DamCB/mu_spim/doc/images/all_unzoom.png

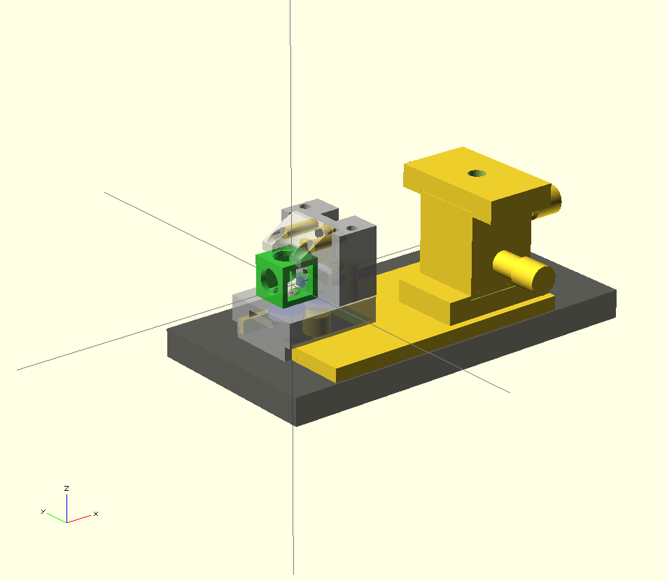
doc/images/all_unzoom.png
