DamCB/mu_spim/doc/images/all_zoom.png

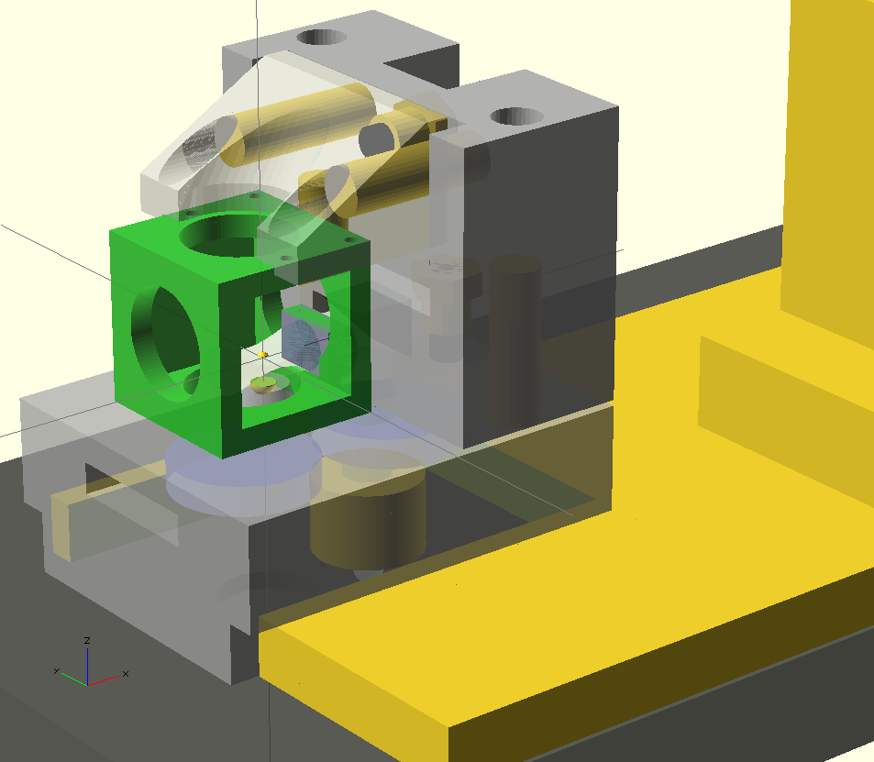
doc/images/all_zoom.png
