DamCB/mu_spim/doc/images/IMGP2774.JPG

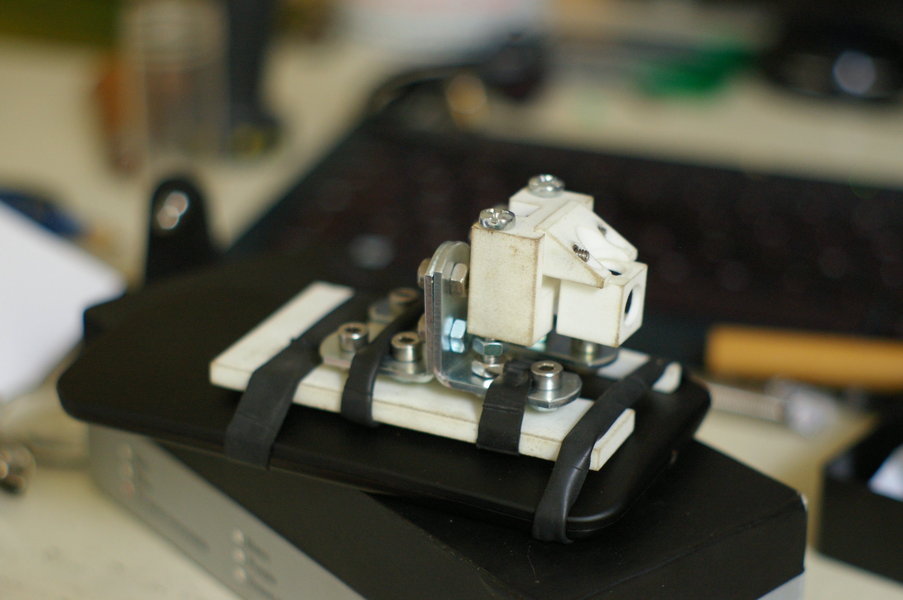
doc/images/IMGP2774.JPG
