DamCB/mu_spim/doc/images/IMGP2775.JPG

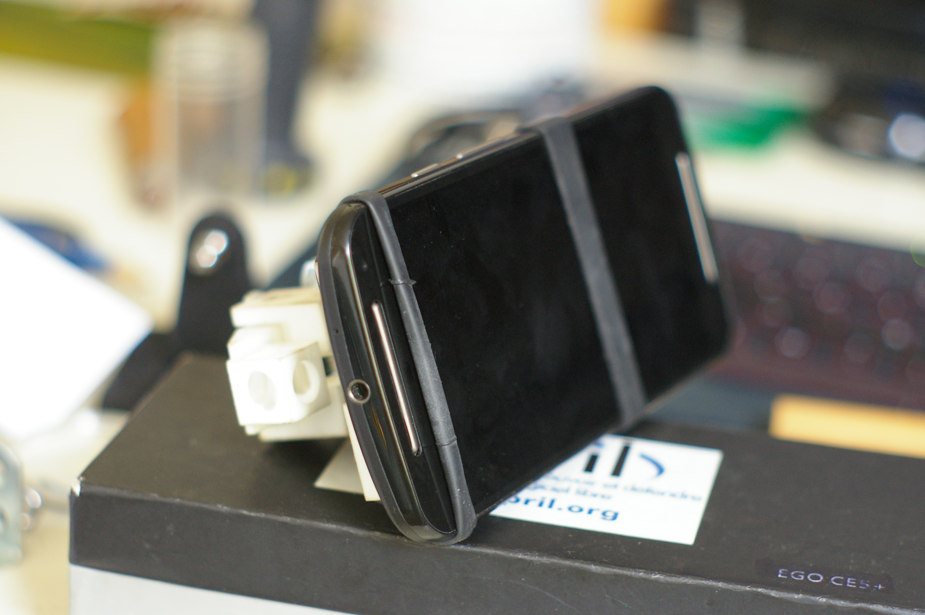
doc/images/IMGP2775.JPG
