DamCB/mu_spim/doc/images/IMGP2776.JPG

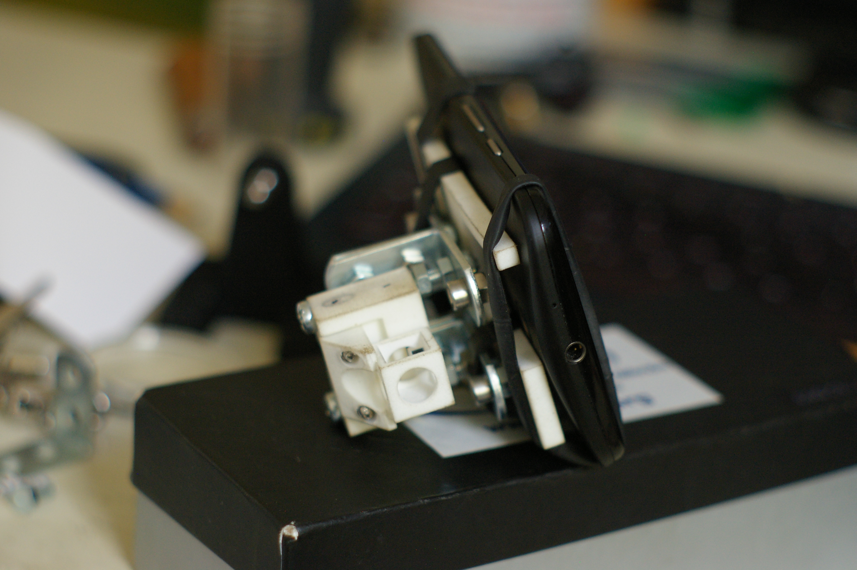
doc/images/IMGP2776.JPG
