DamCB/mu_spim/doc/images/IMGP2777.JPG

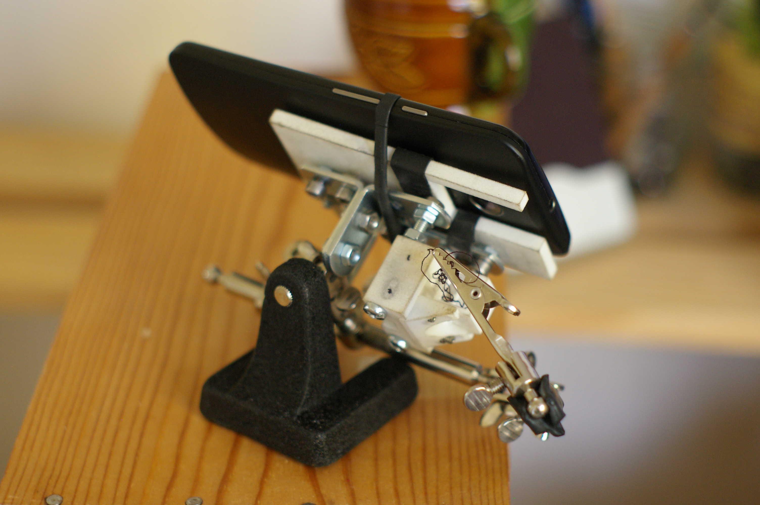
doc/images/IMGP2777.JPG
