DamCB/mu_spim/doc/images/IMGP2778.JPG

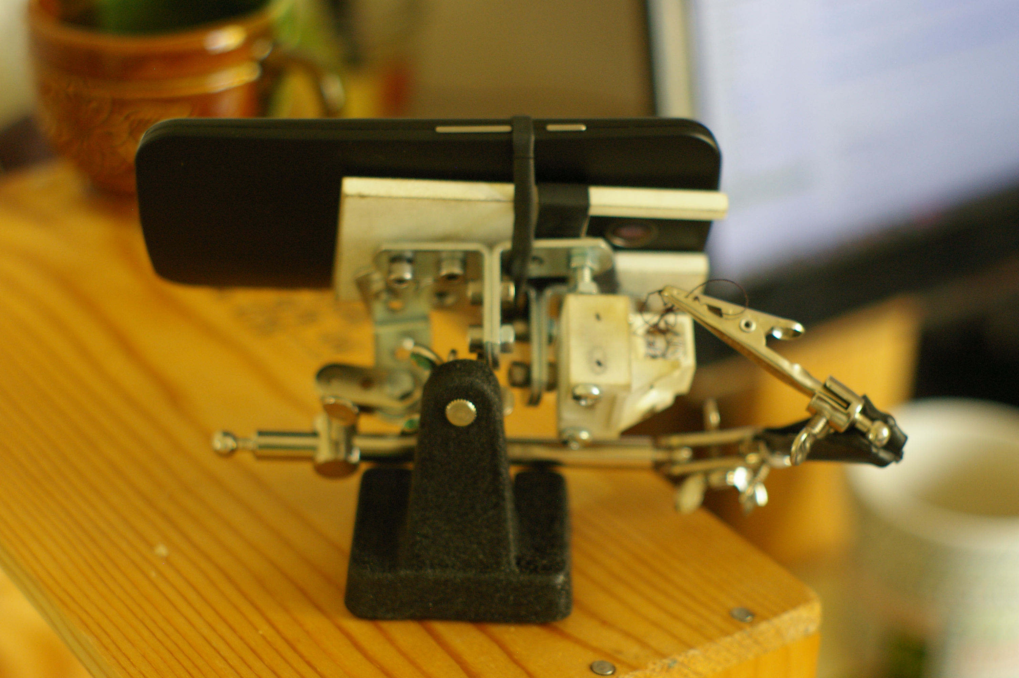
doc/images/IMGP2778.JPG
