DamCB/mu_spim/doc/images/IMGP2779.JPG

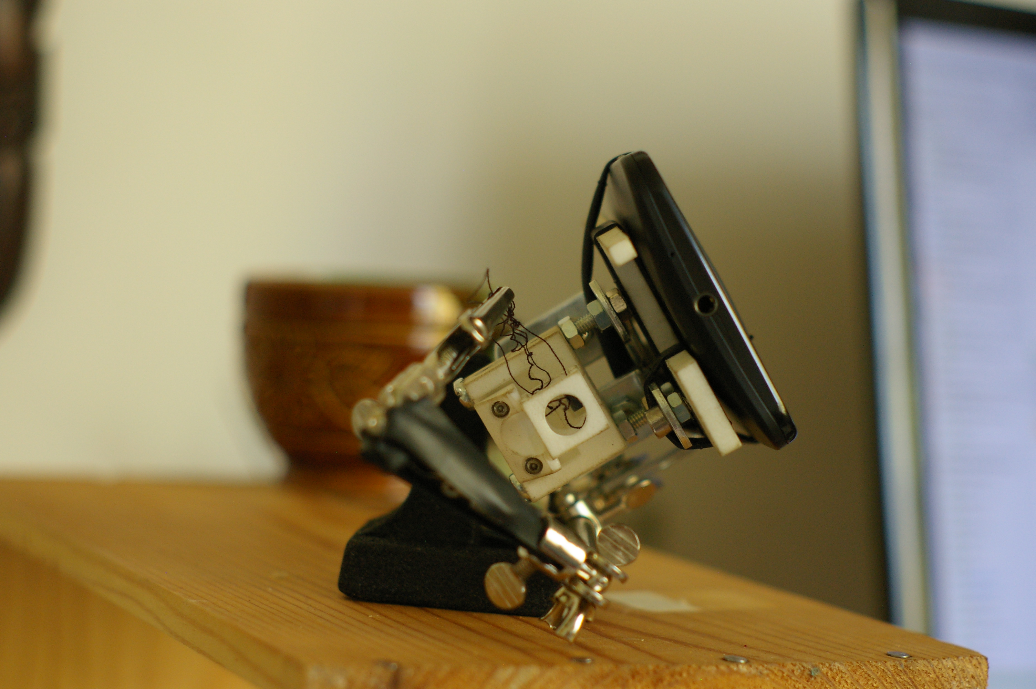
doc/images/IMGP2779.JPG
