DamCB/mu_spim/doc/images/IMGP2780.JPG

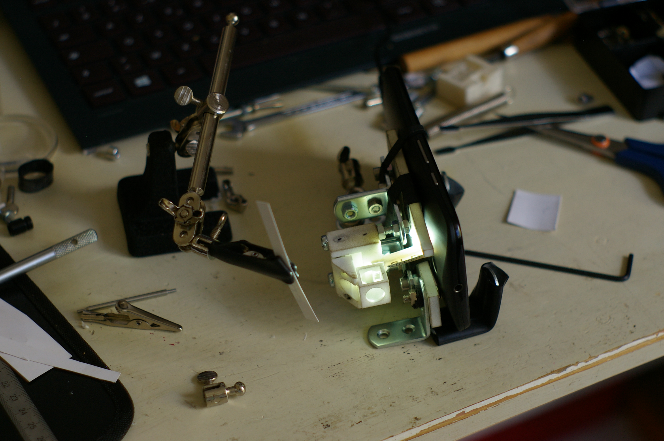
doc/images/IMGP2780.JPG
