DamCB/mu_spim/doc/images/IMGP2781.JPG

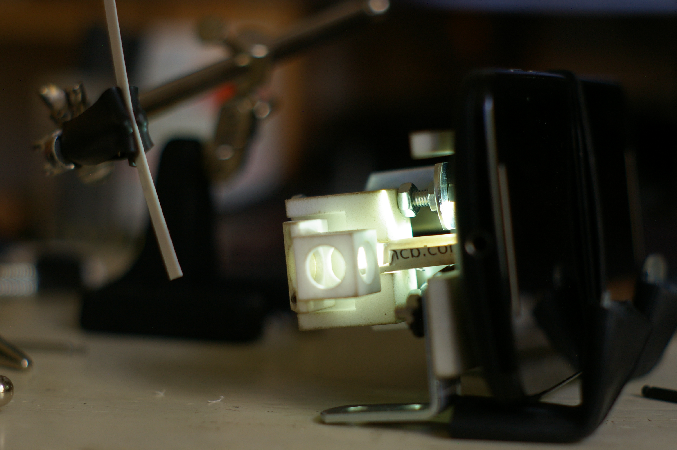
doc/images/IMGP2781.JPG
