DamCB/mu_spim/doc/images/IMGP2782.JPG

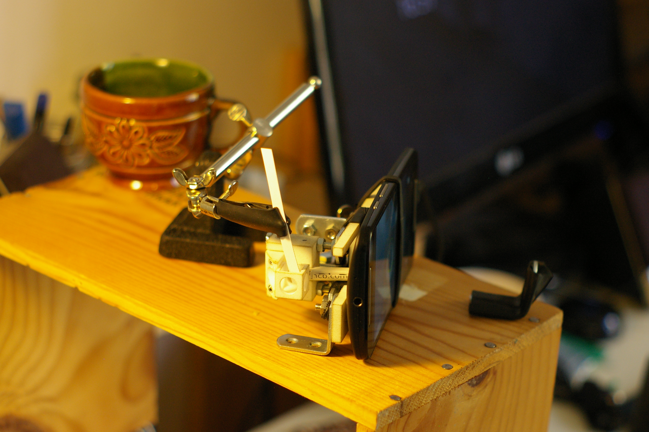
doc/images/IMGP2782.JPG
