DamCB/mu_spim/doc/images/IMGP2783.JPG

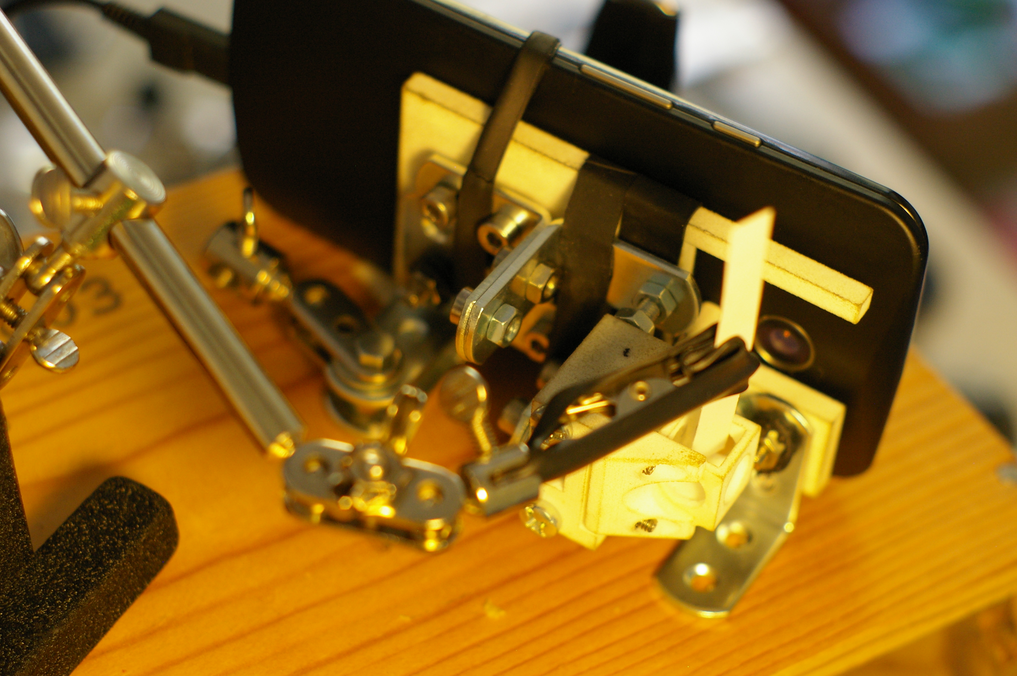
doc/images/IMGP2783.JPG
