DamCB/mu_spim/doc/images/IMGP2784.JPG

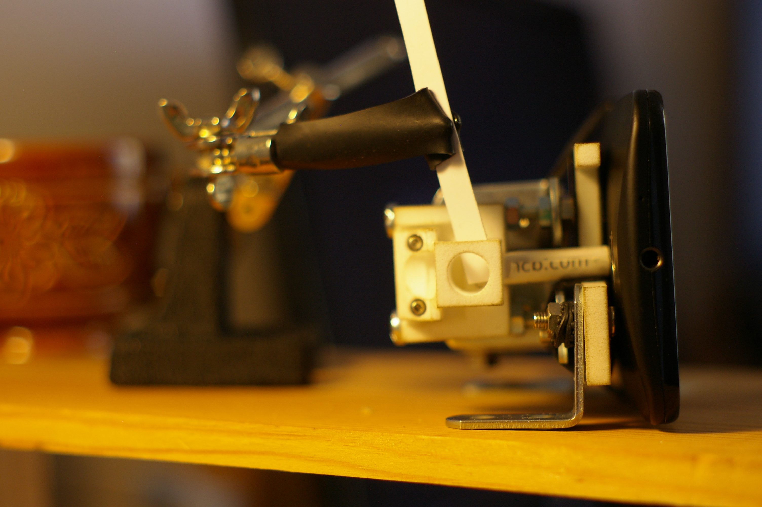
doc/images/IMGP2784.JPG
