DamCB/mu_spim/doc/images/IMGP2785.JPG

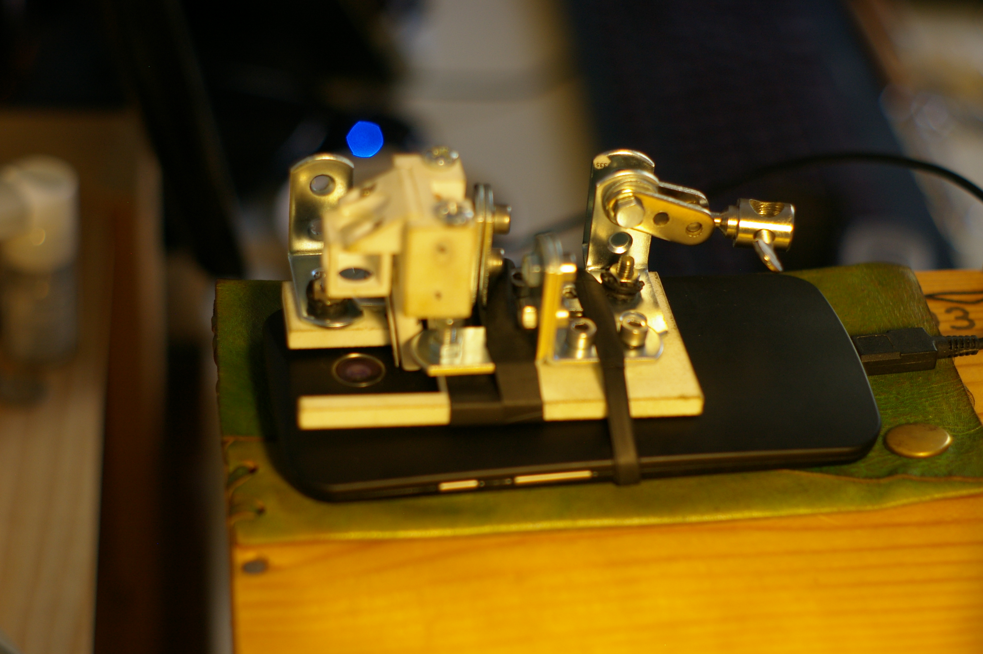
doc/images/IMGP2785.JPG
