DamCB/mu_spim/doc/images/IMGP2786.JPG

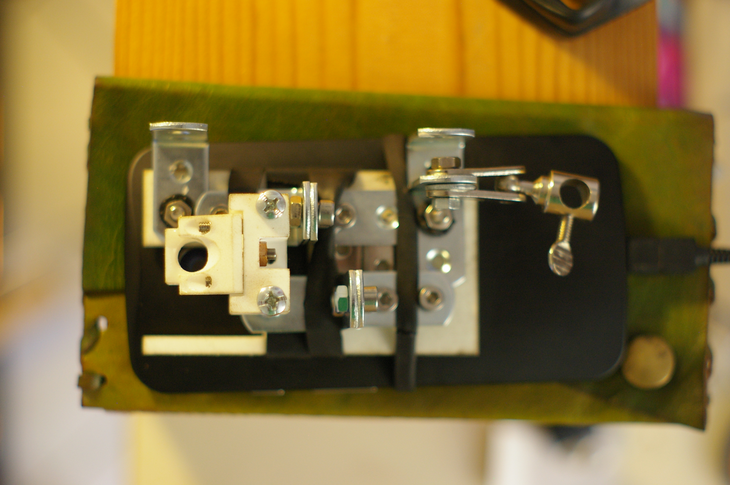
doc/images/IMGP2786.JPG
