DamCB/mu_spim/doc/images/IMGP2787.JPG

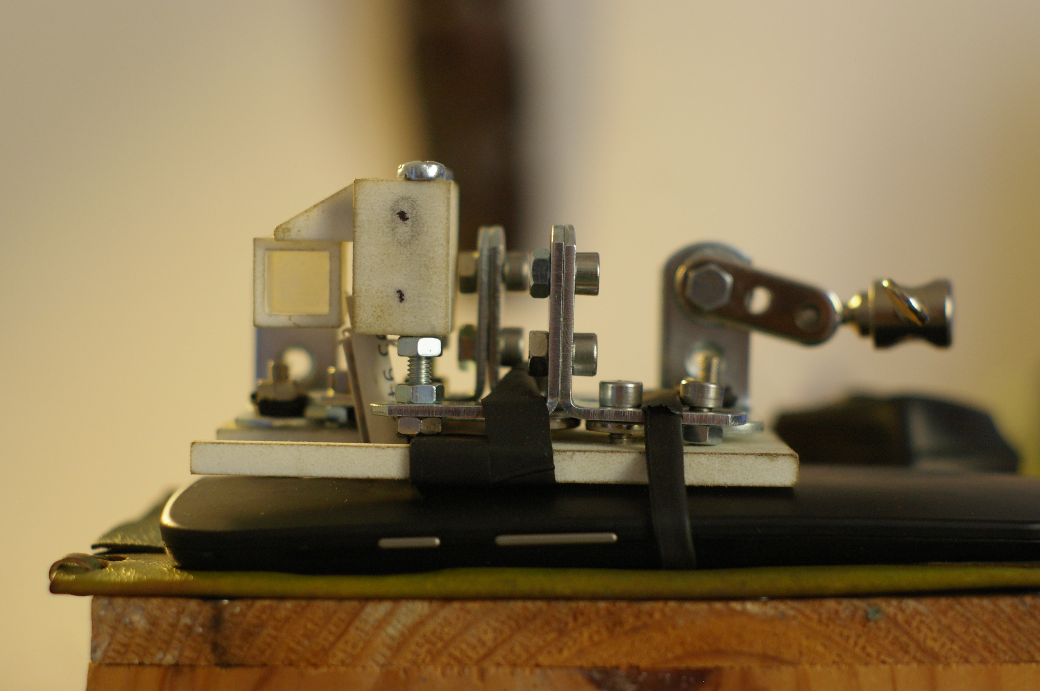
doc/images/IMGP2787.JPG
