DamCB/mu_spim/doc/images/IMGP2788.JPG

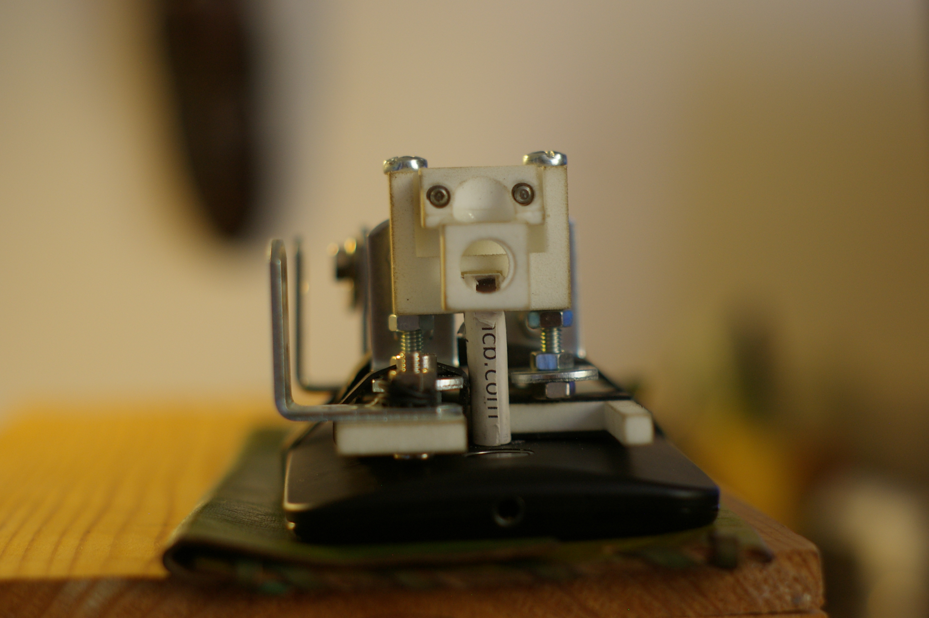
doc/images/IMGP2788.JPG
