DamCB/mu_spim/doc/images/IMGP2790.JPG

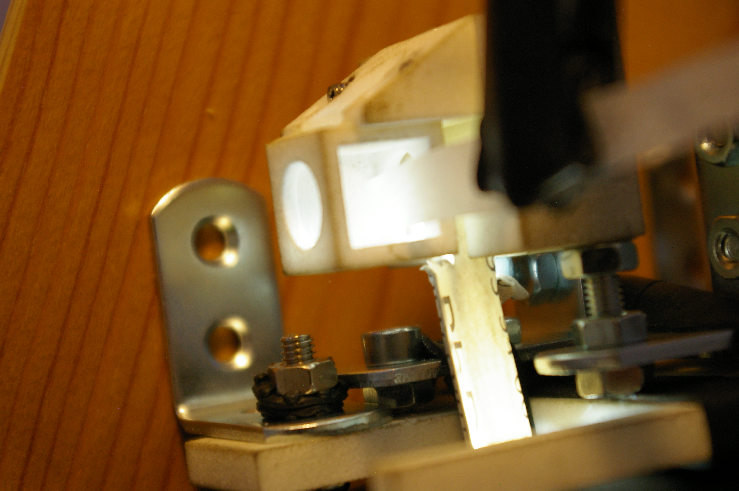
doc/images/IMGP2790.JPG
