DamCB/mu_spim/doc/images/IMGP2791.JPG

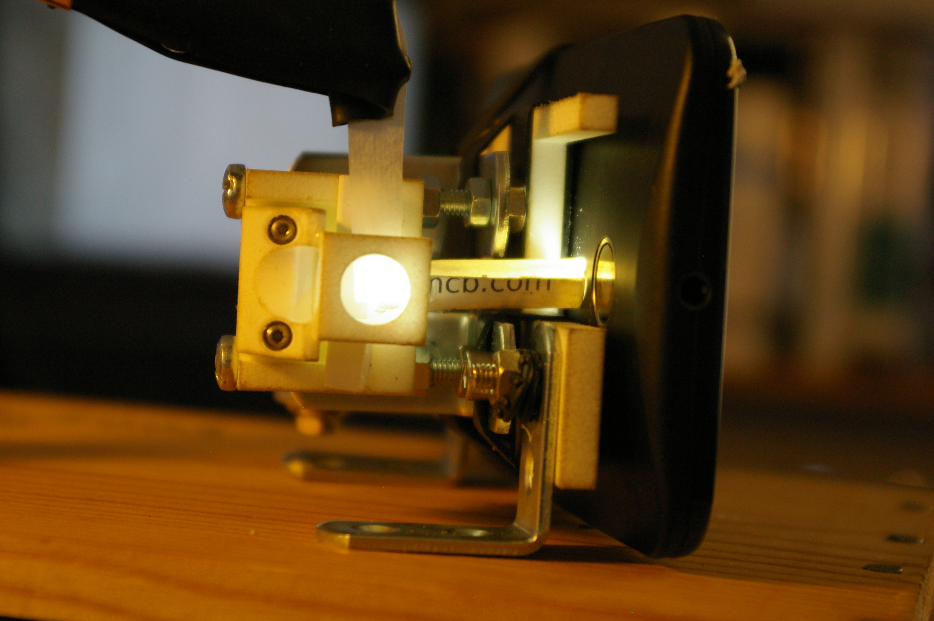
doc/images/IMGP2791.JPG
