DamCB/mu_spim/doc/images/IMGP2793.JPG

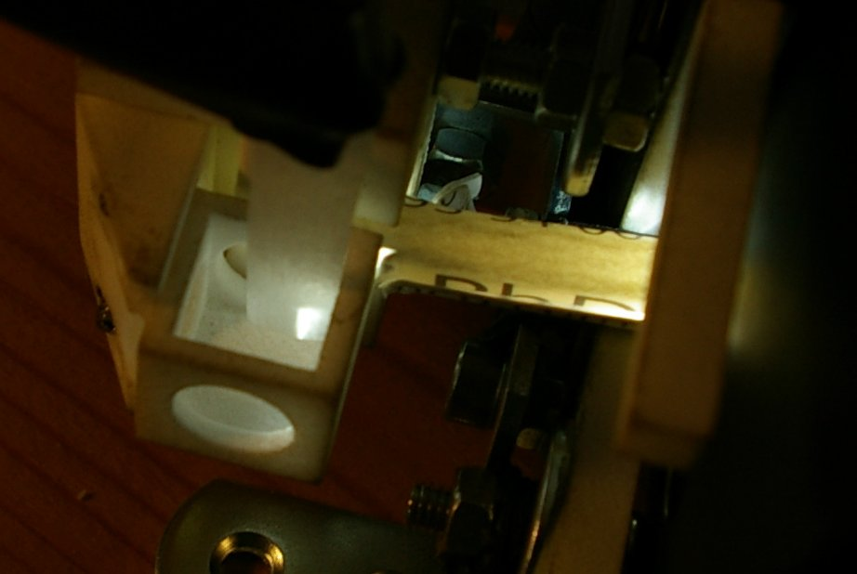
doc/images/IMGP2793.JPG
