DamCB/mu_spim/phone/moto_g_4g.jpeg

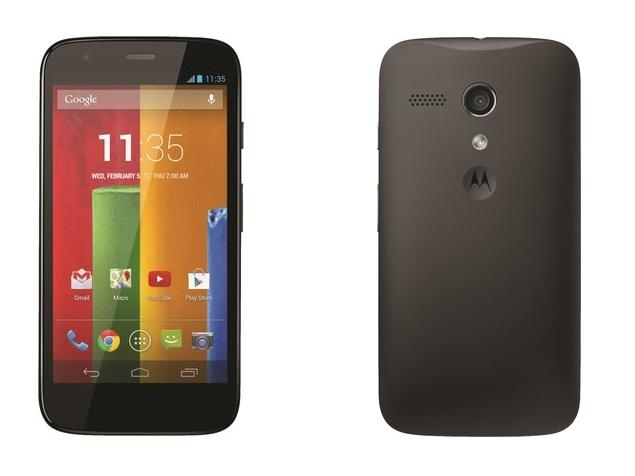
phone/moto_g_4g.jpeg
