DamCB/mu_spim/phone/motorola-moto-g-4g-2015-back.jpg

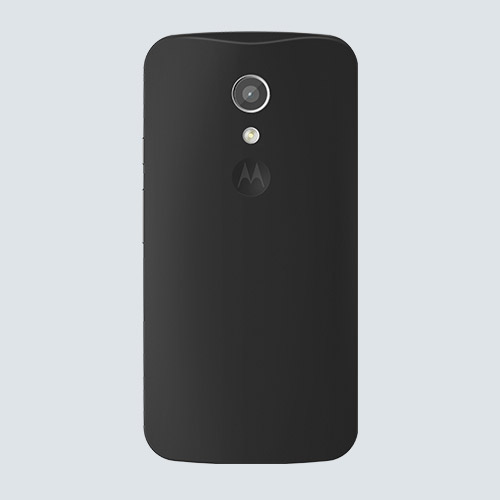
phone/motorola-moto-g-4g-2015-back.jpg
