DamCB/mu_spim/open_scad/parts/step_45933.stp

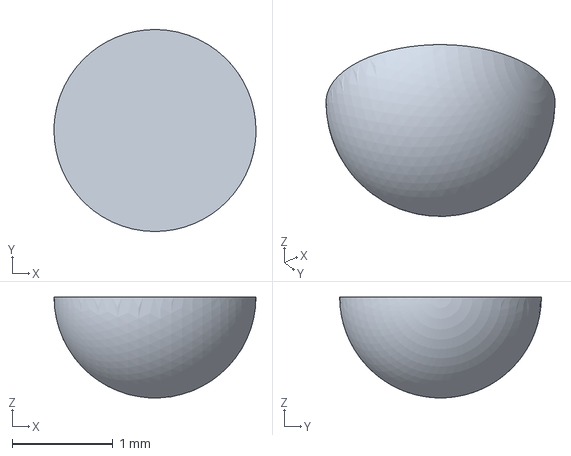
[picture p51: CAD file, 2015-09-04]
open_scad/parts/step_45933.stp
2.00 x 2.00 x 0.999 mm
