DamCB/mu_spim/open_scad/parts/LJ1918L1-A-Step.step

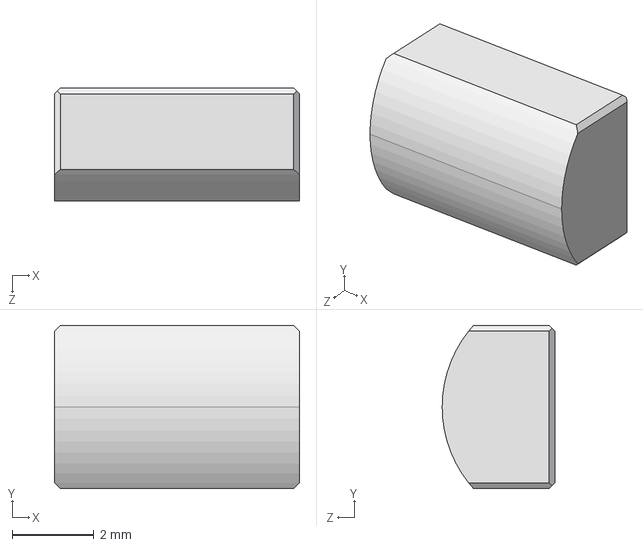
[picture p52: CAD file, 2015-09-04]
open_scad/parts/LJ1918L1-A-Step.step
6.00 x 4.00 x 2.76 mm
