DamCB/mu_spim/open_scad/parts/LJ1918L1-A-AutoCADDXF.dxf

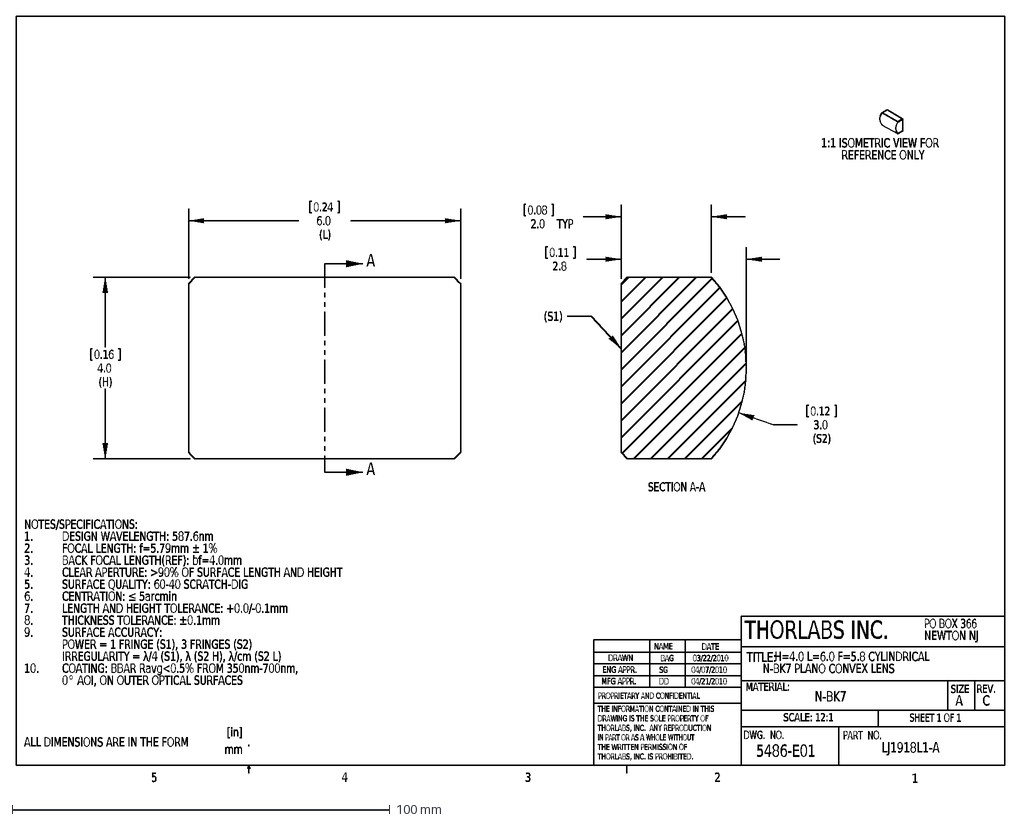
[picture p53: CAD file, 2015-09-04]
open_scad/parts/LJ1918L1-A-AutoCADDXF.dxf
5
4
3
2
1
MATERIAL:
PART NO.
PROPRIETARY AND CONFIDENTIAL
DRAWN
ENG APPR.
MFG APPR.
NAME
TITLE:
SIZE
A
REV.
SCALE: 12:1
SHEET 1 OF 1
5486-E01
THE INFORMATION CONTAINED IN THIS
DRAWING IS THE SOLE PROPERTY OF
THORLABS, INC. ANY REPRODUCTION
IN PART OR AS A WHOLE WITHOUT
THE WRITTEN PERMISSION OF
THORLABS, INC. IS PROHIBITED.
DWG. NO.
DATE
THORLABS INC.
PO BOX 366
NEWTON NJ
ALL DIMENSIONS ARE IN THE FORM
[in]
mm
.
BAG
03/22/2010
H=4.0 L=6.0 F=5.8 CYLINDRICAL
N-BK7 PLANO CONVEX LENS
N-BK7
LJ1918L1-A
NOTES/SPECIFICATIONS:
DESIGN WAVELENGTH: 587.6nm
1.
FOCAL LENGTH: f=5.79mm ± 1%
2.
BACK FOCAL LENGTH(REF): bf=4.0mm
3.
CLEAR APERTURE: >90% OF SURFACE LENGTH AND HEIGHT
4.
SURFACE QUALITY: 60-40 SCRATCH-DIG
5.
CENTRATION: ≤ 5arcmin
6.
LENGTH AND HEIGHT TOLERANCE: +0.0/-0.1mm
7.
THICKNESS TOLERANCE: ±0.1mm
8.
SURFACE ACCURACY:
9.
POWER = 1 FRINGE (S1), 3 FRINGES (S2)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
