DamCB/mu_spim/open_scad/stl_optics_plate.scad

include <base_dimensions.scad>;
use <chamber.scad>;

use <optic_blocks.scad>;
use <base.scad>;

optics_plate();
